Elvin-Wu/backlit-pcb-art-lamp/Images/Featured/Main-Board_Powered.jpg

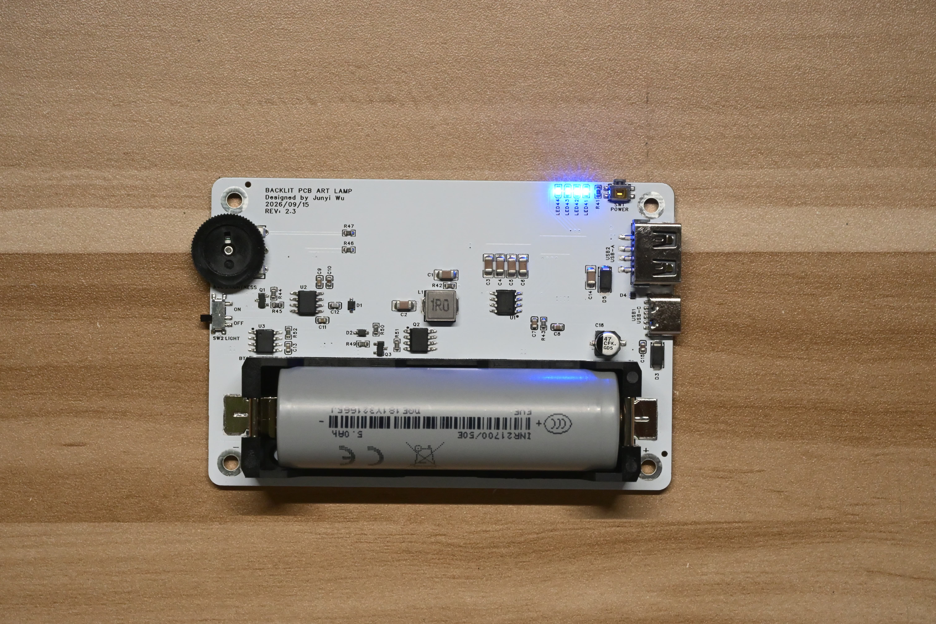
Images/Featured/Main-Board_Powered.jpg
