Elvin-Wu/backlit-pcb-art-lamp/Images/Gallery/DSC_2467.jpg

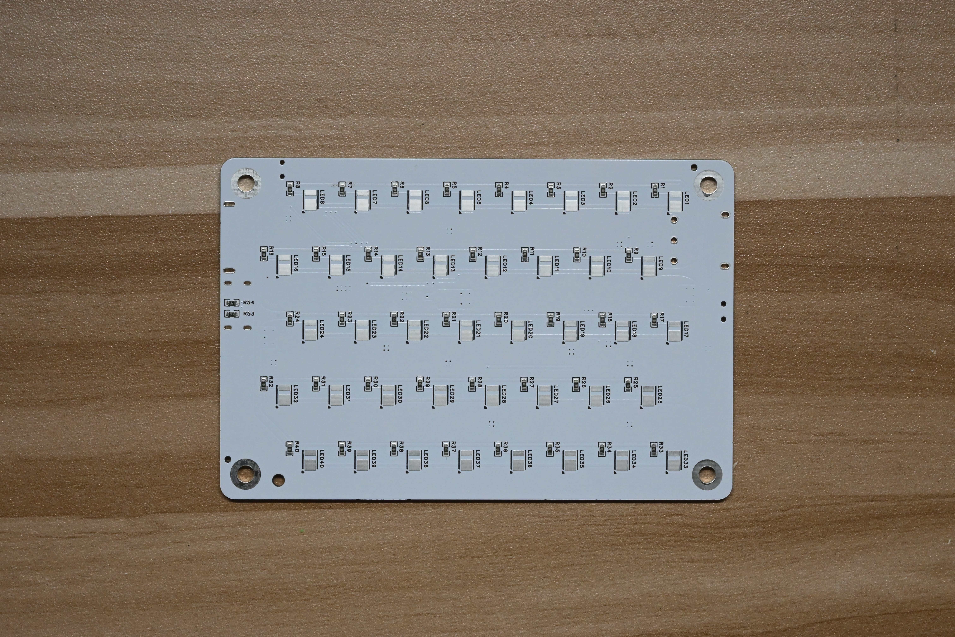
Images/Gallery/DSC_2467.jpg
