Elvin-Wu/backlit-pcb-art-lamp/Images/Gallery/DSC_2468.jpg

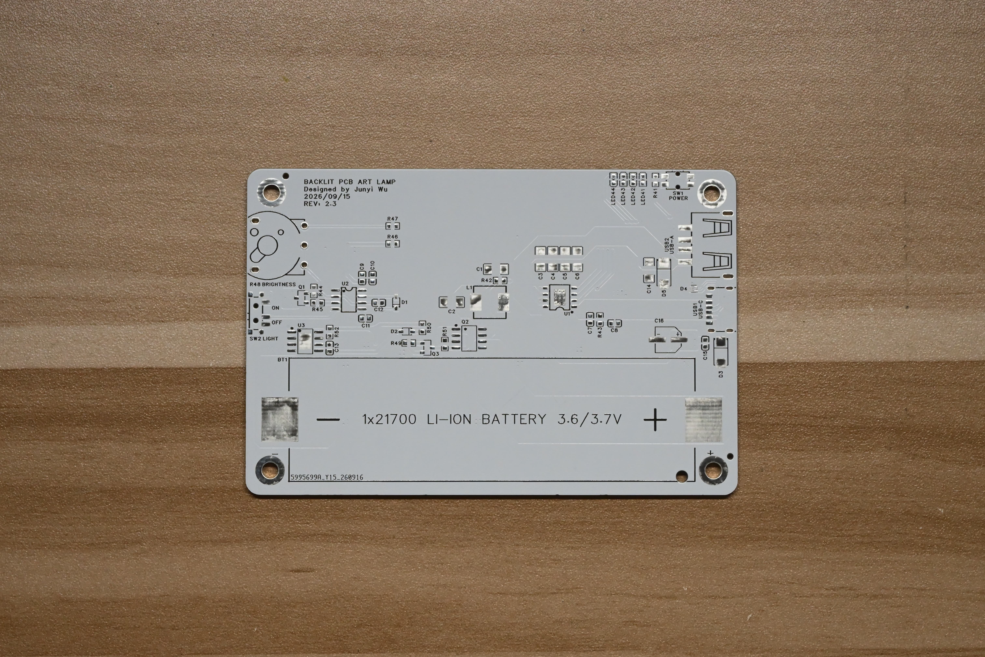
Images/Gallery/DSC_2468.jpg
