Elvin-Wu/backlit-pcb-art-lamp/Images/Gallery/DSC_2469.jpg

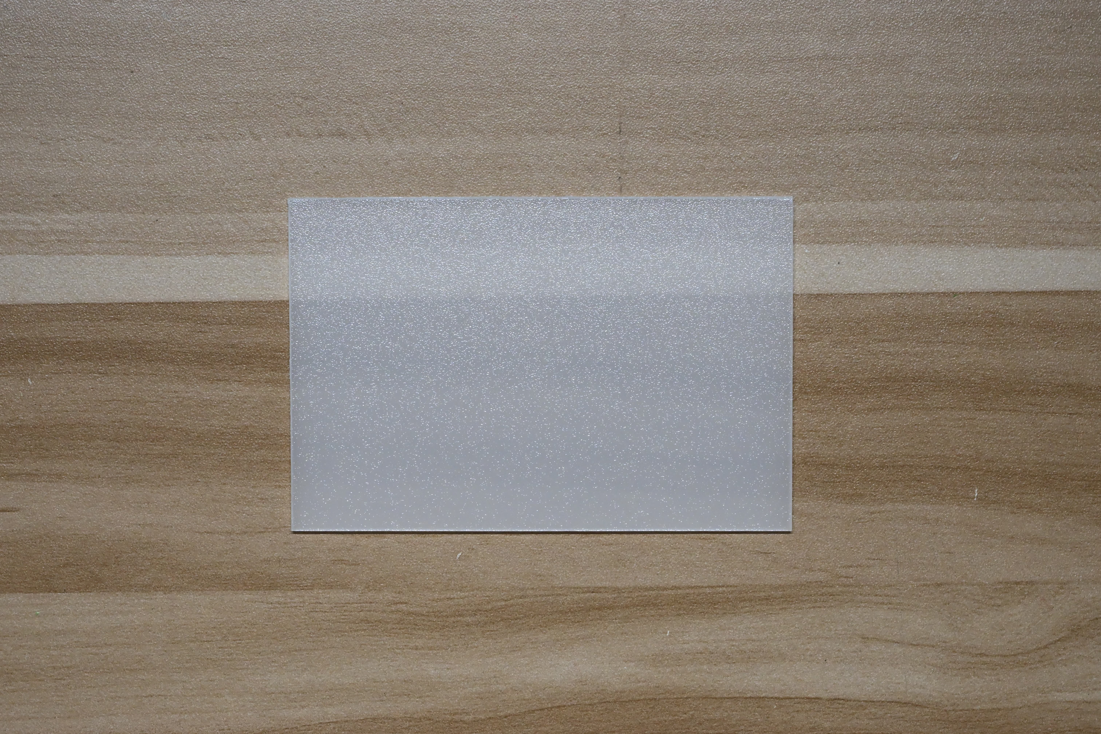
Images/Gallery/DSC_2469.jpg
