Elvin-Wu/backlit-pcb-art-lamp/Images/Gallery/DSC_2470.jpg

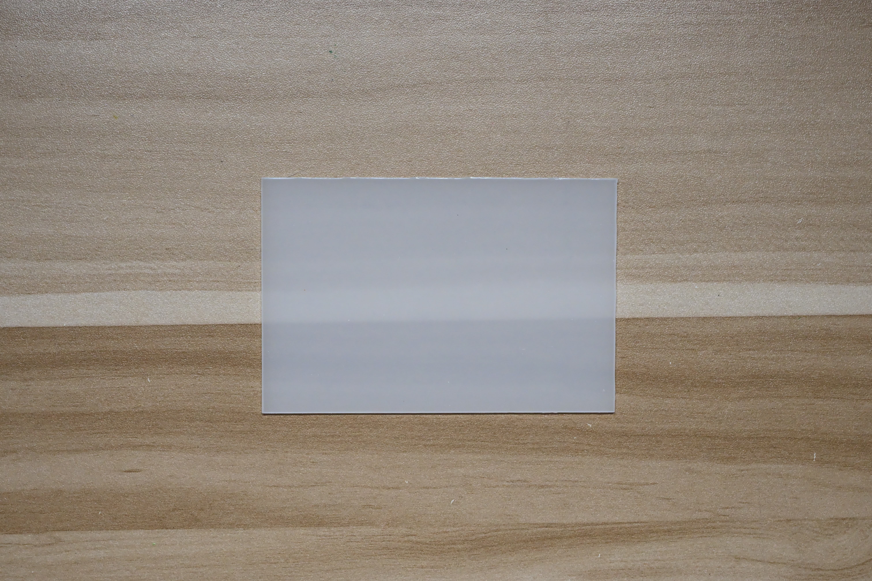
Images/Gallery/DSC_2470.jpg
