Elvin-Wu/backlit-pcb-art-lamp/Images/Gallery/DSC_2472.jpg

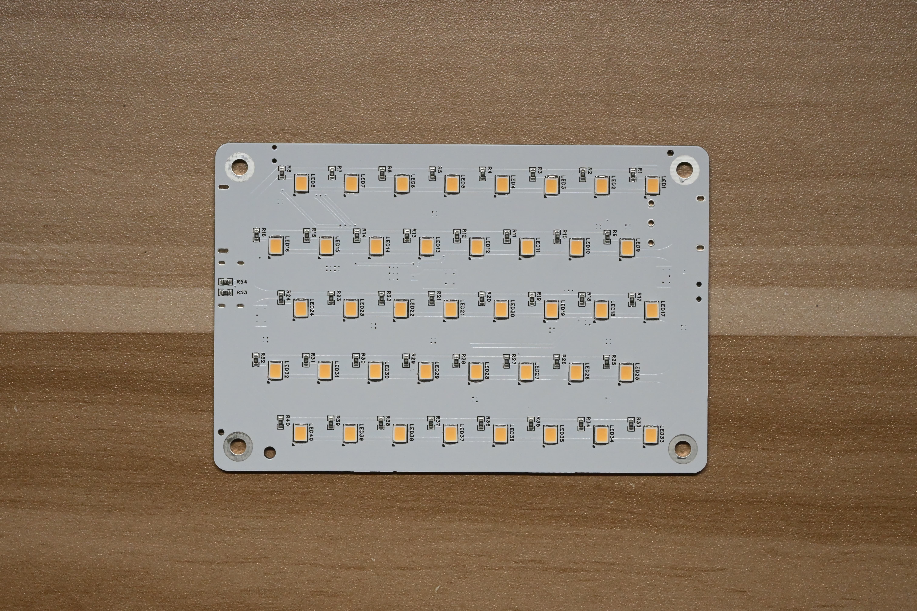
Images/Gallery/DSC_2472.jpg
