Elvin-Wu/backlit-pcb-art-lamp/Images/Gallery/DSC_2473.jpg

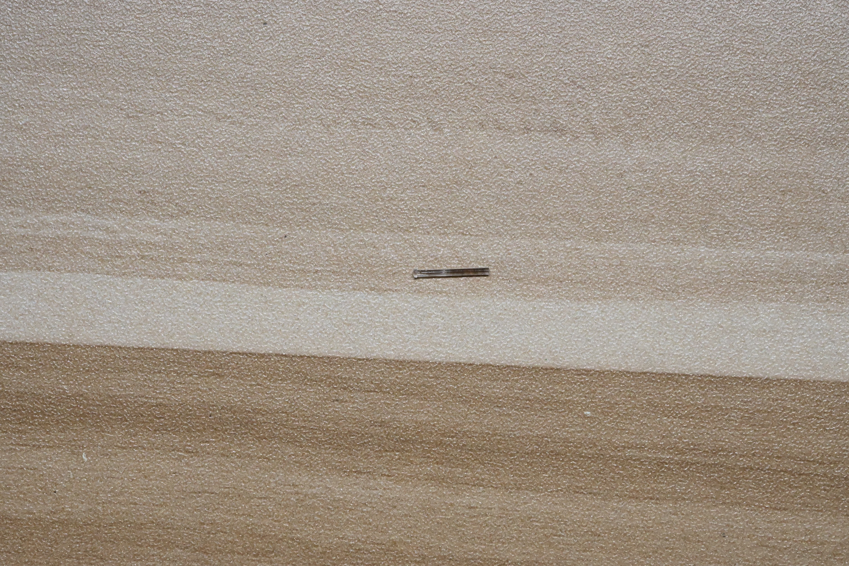
Images/Gallery/DSC_2473.jpg
