Elvin-Wu/backlit-pcb-art-lamp/Images/Gallery/DSC_2474.jpg

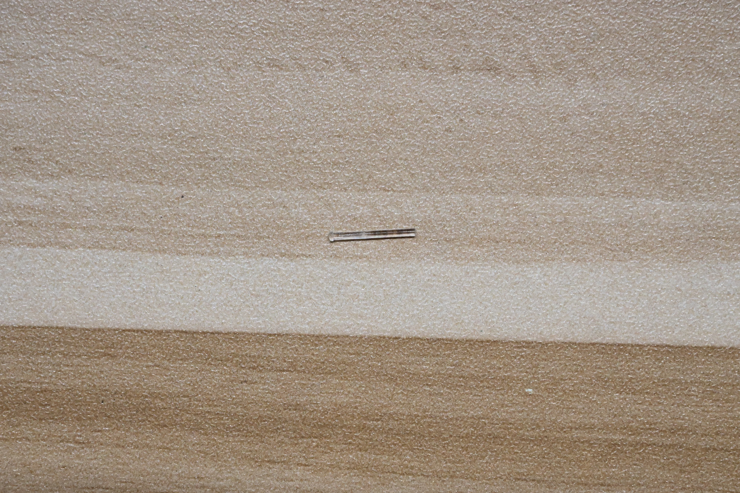
Images/Gallery/DSC_2474.jpg
