Elvin-Wu/backlit-pcb-art-lamp/Images/Gallery/DSC_2475.jpg

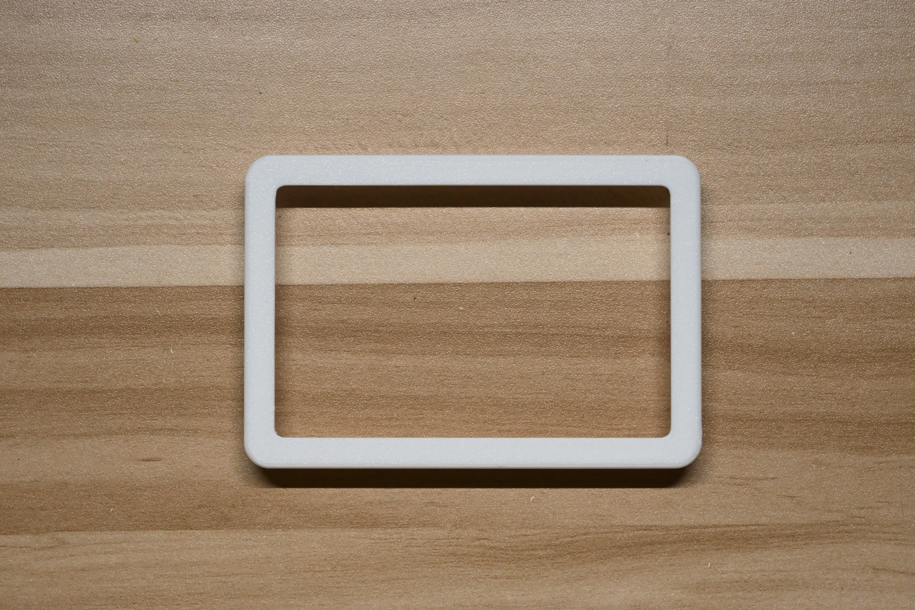
Images/Gallery/DSC_2475.jpg
