Elvin-Wu/backlit-pcb-art-lamp/Images/Gallery/DSC_2476.jpg

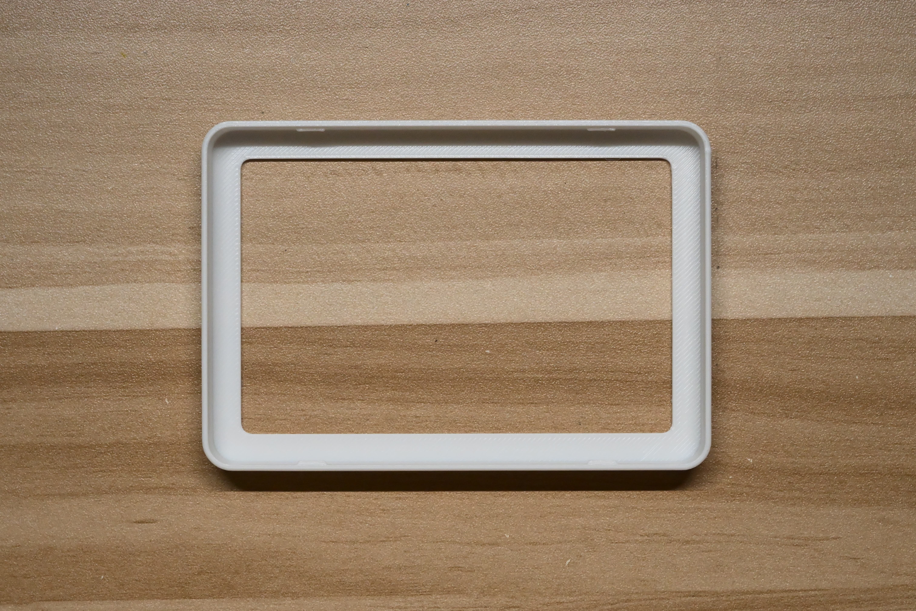
Images/Gallery/DSC_2476.jpg
