Elvin-Wu/backlit-pcb-art-lamp/Images/Gallery/DSC_2478.jpg

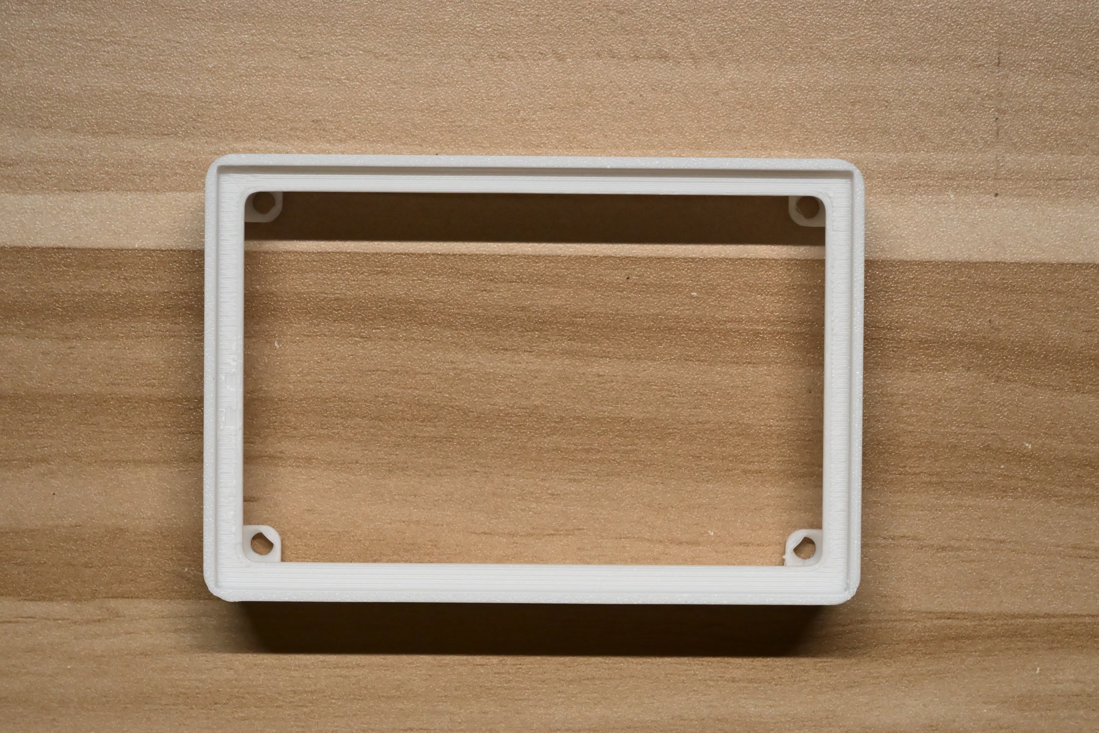
Images/Gallery/DSC_2478.jpg
