Elvin-Wu/backlit-pcb-art-lamp/Images/Gallery/DSC_2479.jpg

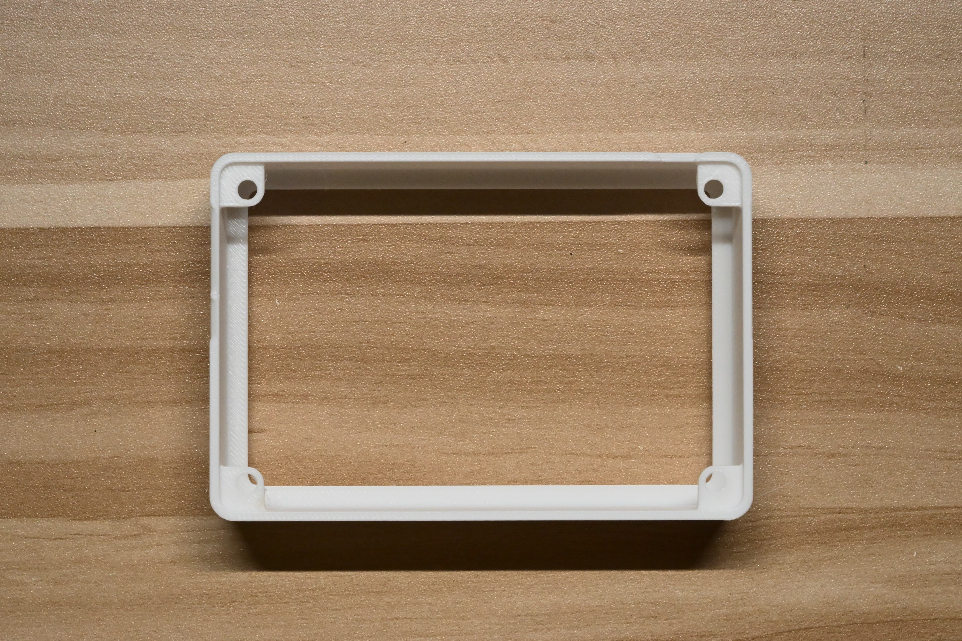
Images/Gallery/DSC_2479.jpg
