Elvin-Wu/backlit-pcb-art-lamp/Images/Gallery/DSC_2480.jpg

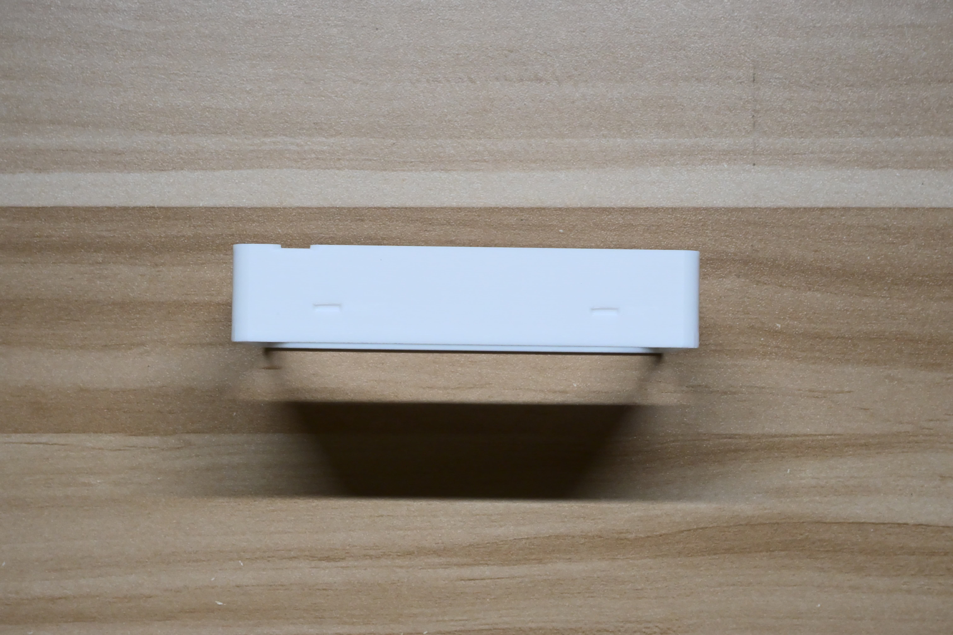
Images/Gallery/DSC_2480.jpg
