Elvin-Wu/backlit-pcb-art-lamp/Images/Gallery/DSC_2481.jpg

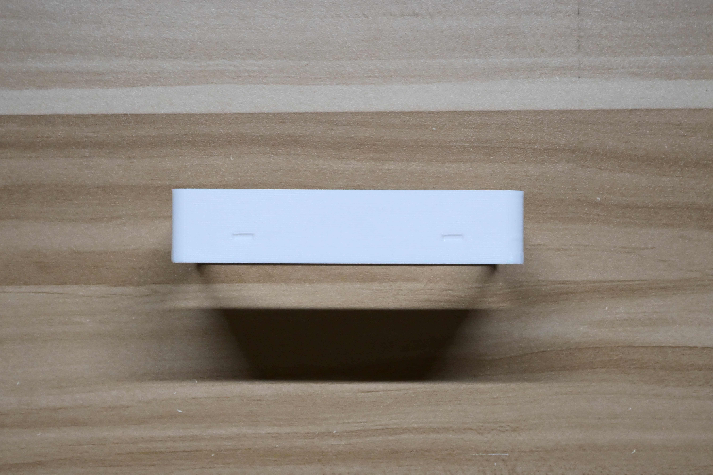
Images/Gallery/DSC_2481.jpg
