Elvin-Wu/backlit-pcb-art-lamp/Images/Gallery/DSC_2482.jpg

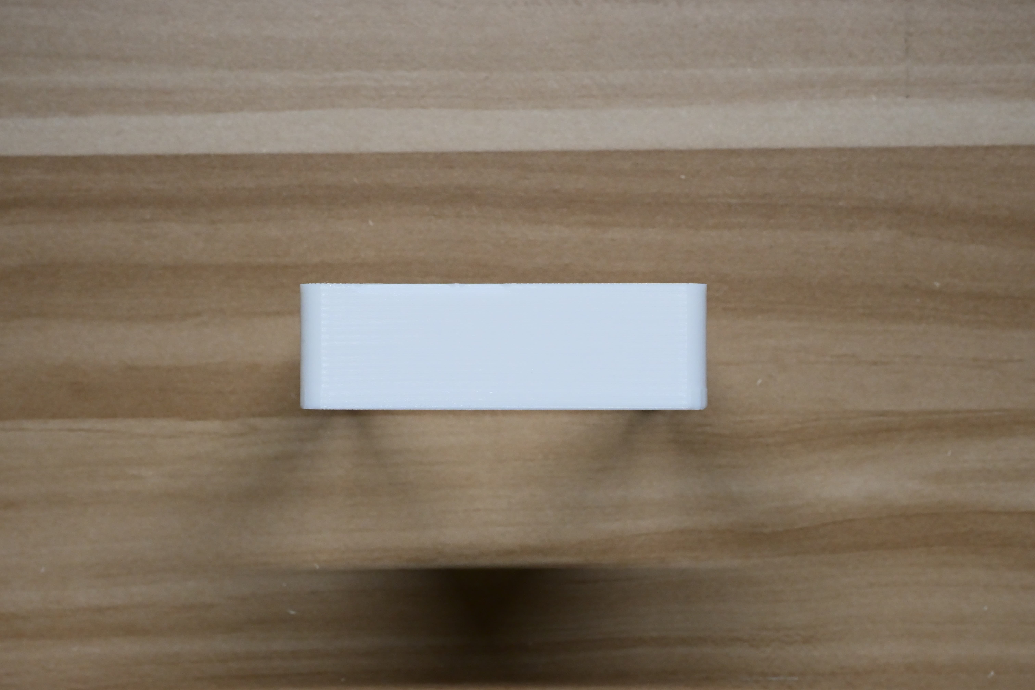
Images/Gallery/DSC_2482.jpg
