Elvin-Wu/backlit-pcb-art-lamp/Images/Gallery/DSC_2483.jpg

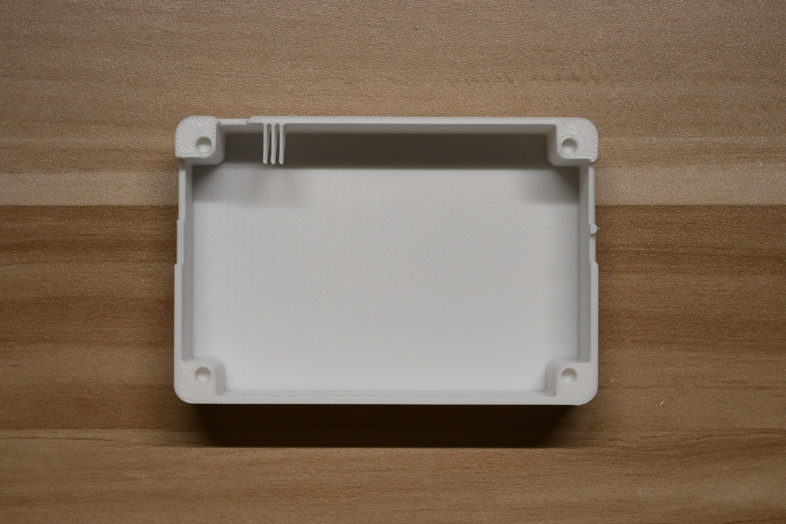
Images/Gallery/DSC_2483.jpg
