Elvin-Wu/backlit-pcb-art-lamp/Images/Gallery/DSC_2484.jpg

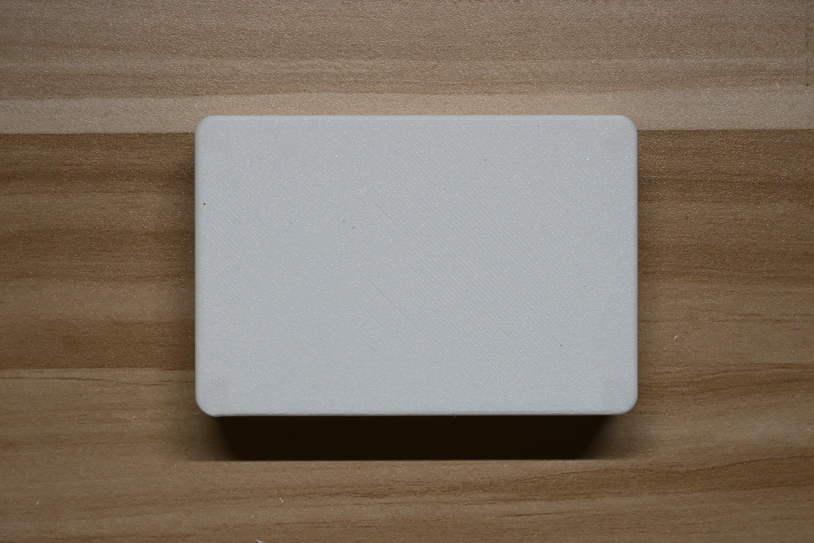
Images/Gallery/DSC_2484.jpg
