Elvin-Wu/backlit-pcb-art-lamp/Images/Gallery/DSC_2485.jpg

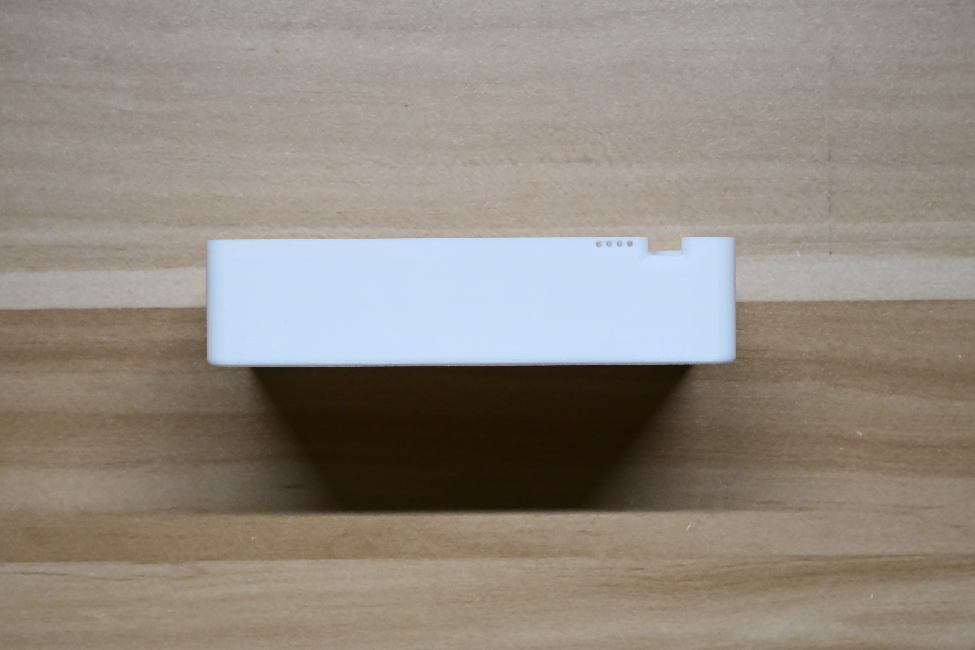
Images/Gallery/DSC_2485.jpg
