Elvin-Wu/backlit-pcb-art-lamp/Images/Gallery/DSC_2486.jpg

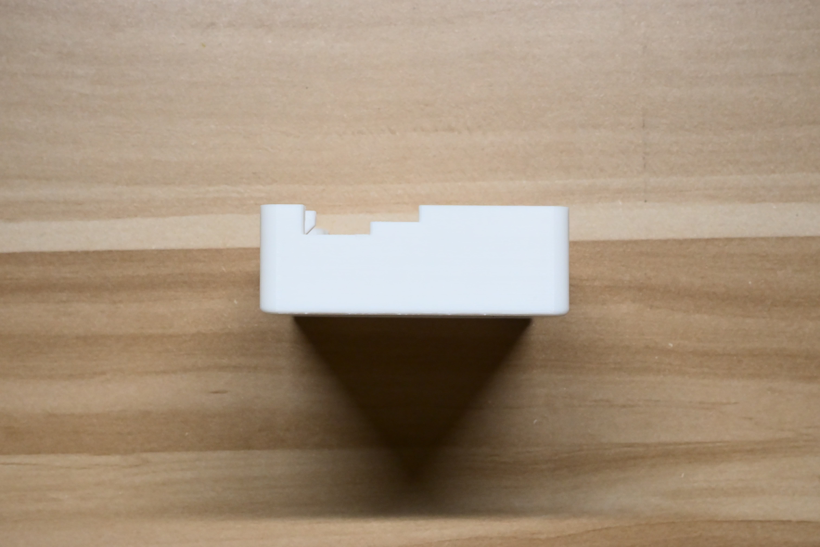
Images/Gallery/DSC_2486.jpg
