Elvin-Wu/backlit-pcb-art-lamp/Images/Gallery/DSC_2487.jpg

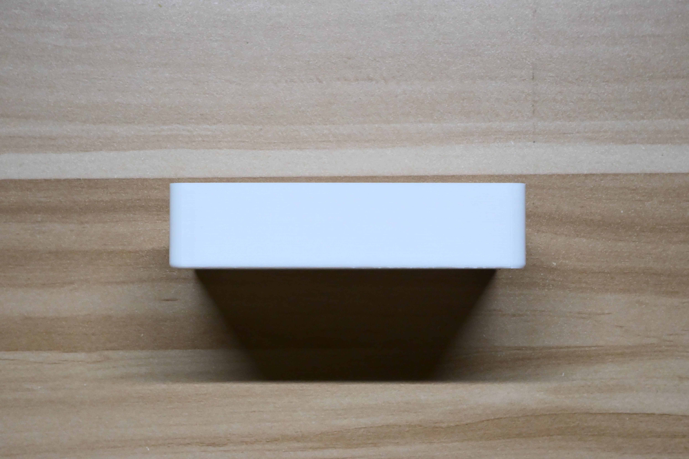
Images/Gallery/DSC_2487.jpg
