Elvin-Wu/backlit-pcb-art-lamp/Images/Gallery/DSC_2488.jpg

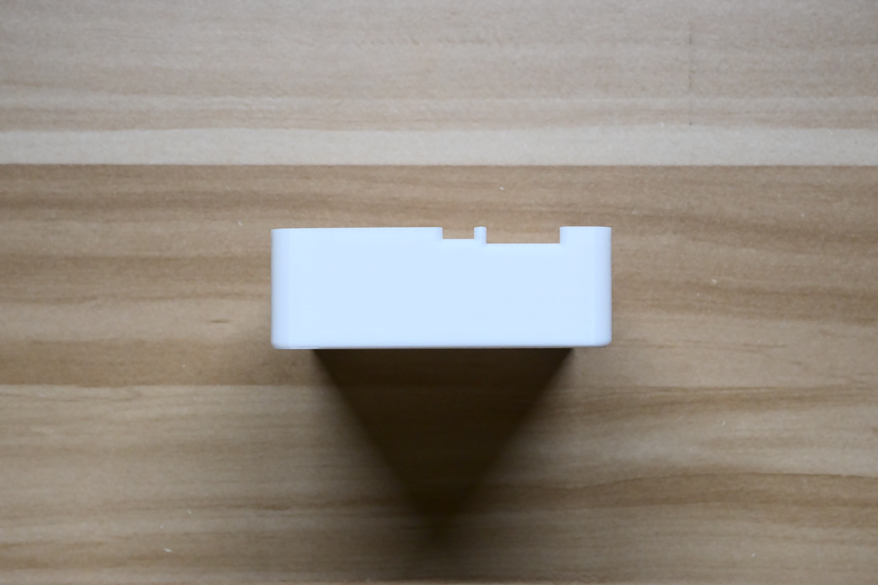
Images/Gallery/DSC_2488.jpg
