Elvin-Wu/backlit-pcb-art-lamp/Images/Gallery/DSC_2490.jpg

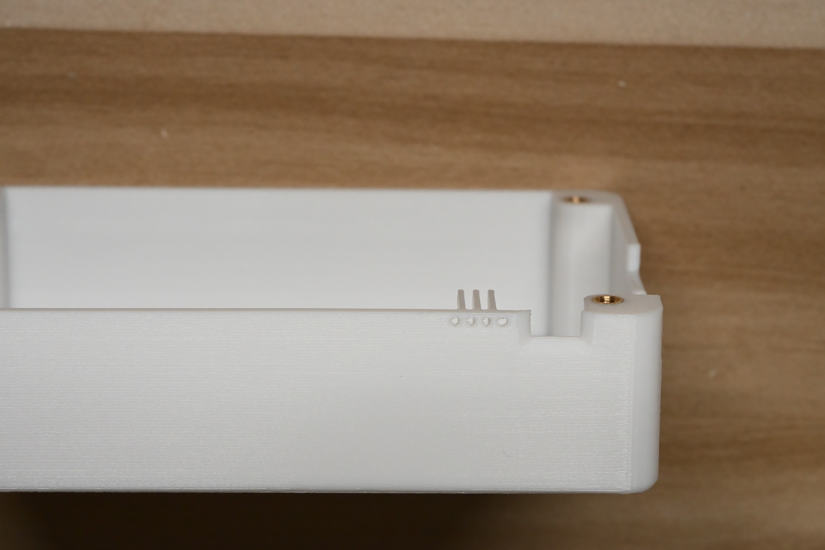
Images/Gallery/DSC_2490.jpg
