Elvin-Wu/backlit-pcb-art-lamp/Images/Gallery/DSC_2497.jpg

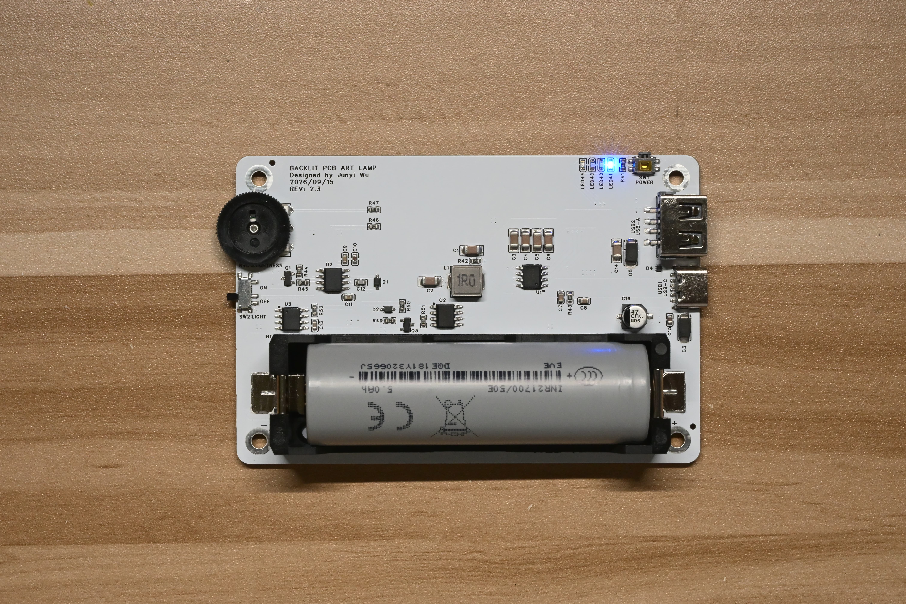
Images/Gallery/DSC_2497.jpg
