Elvin-Wu/backlit-pcb-art-lamp/Images/Gallery/DSC_2500.jpg

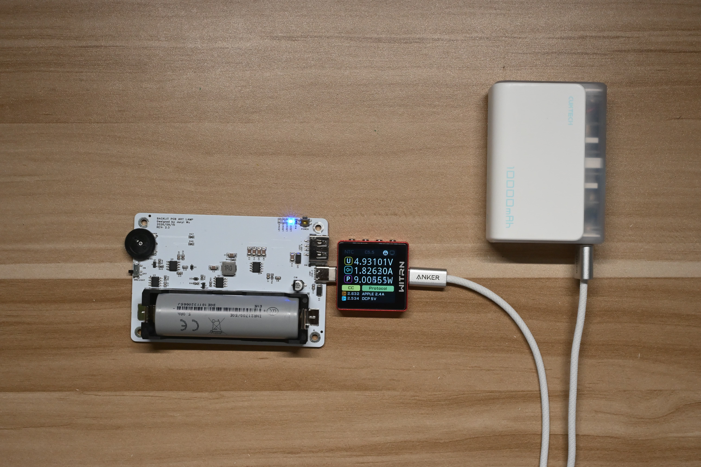
Images/Gallery/DSC_2500.jpg
