Elvin-Wu/backlit-pcb-art-lamp/Images/Gallery/DSC_2501.jpg

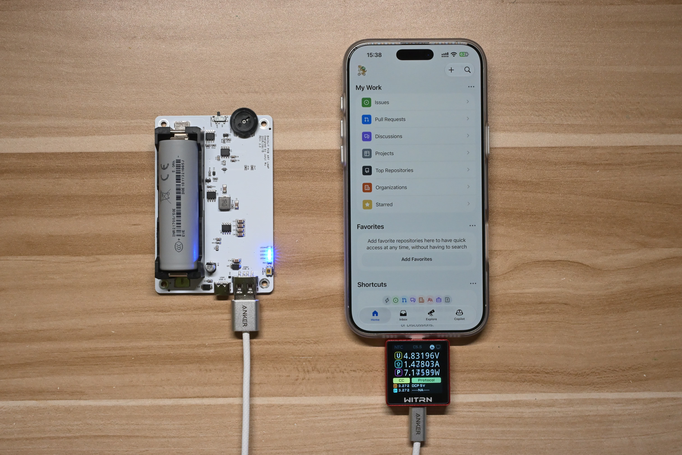
Images/Gallery/DSC_2501.jpg
