Elvin-Wu/backlit-pcb-art-lamp/Images/Gallery/DSC_2503.jpg

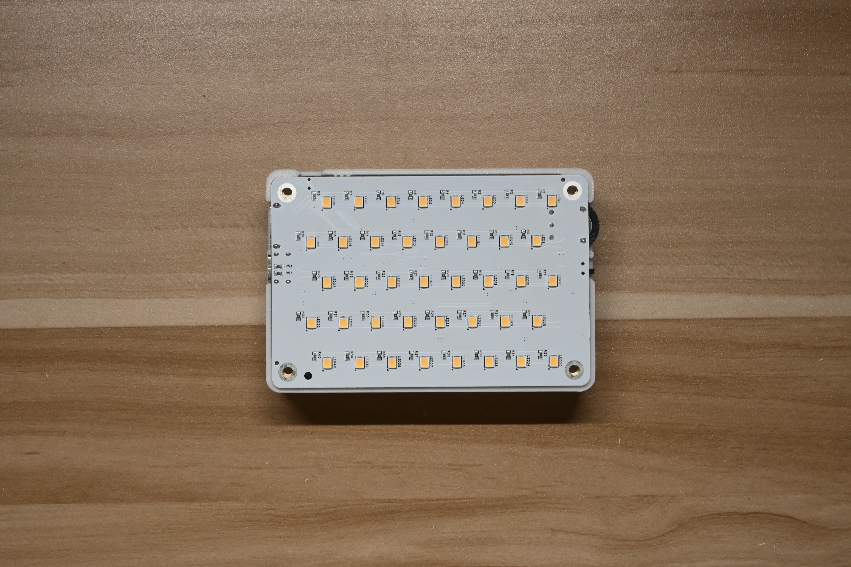
Images/Gallery/DSC_2503.jpg
