Elvin-Wu/backlit-pcb-art-lamp/Images/Gallery/DSC_2505.jpg

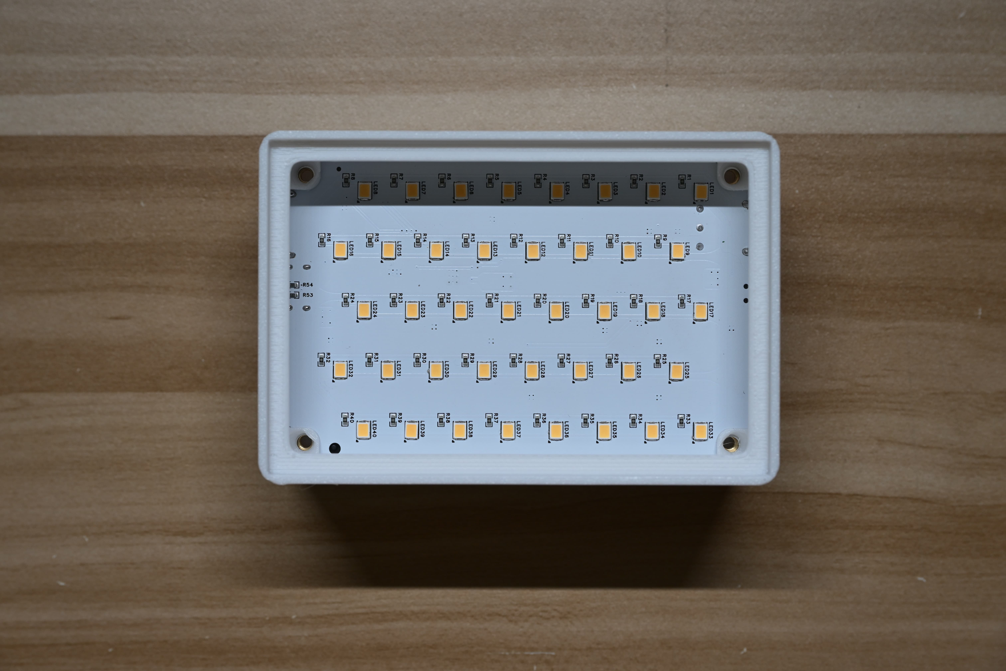
Images/Gallery/DSC_2505.jpg
