Elvin-Wu/backlit-pcb-art-lamp/Images/Gallery/DSC_2507.jpg

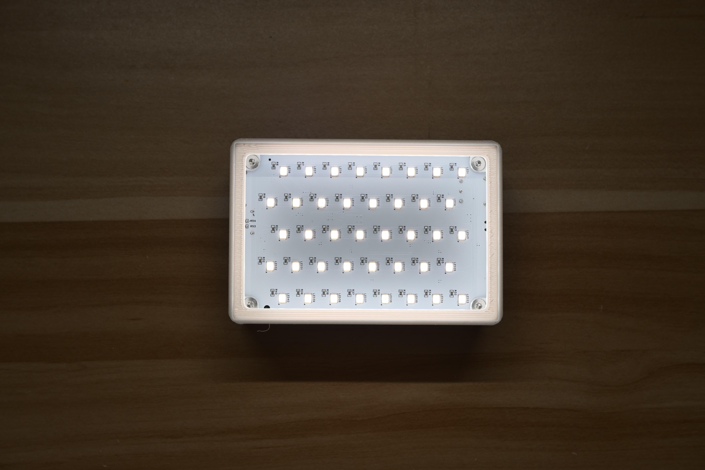
Images/Gallery/DSC_2507.jpg
