Elvin-Wu/backlit-pcb-art-lamp/Images/Gallery/DSC_2509.jpg

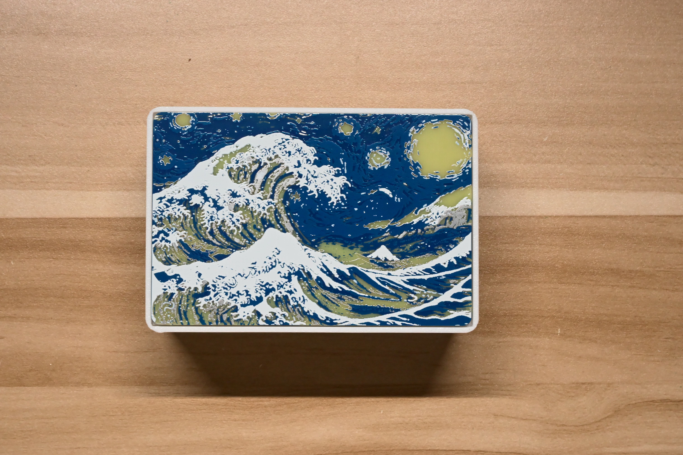
Images/Gallery/DSC_2509.jpg
