Elvin-Wu/backlit-pcb-art-lamp/Images/Gallery/DSC_2516.jpg

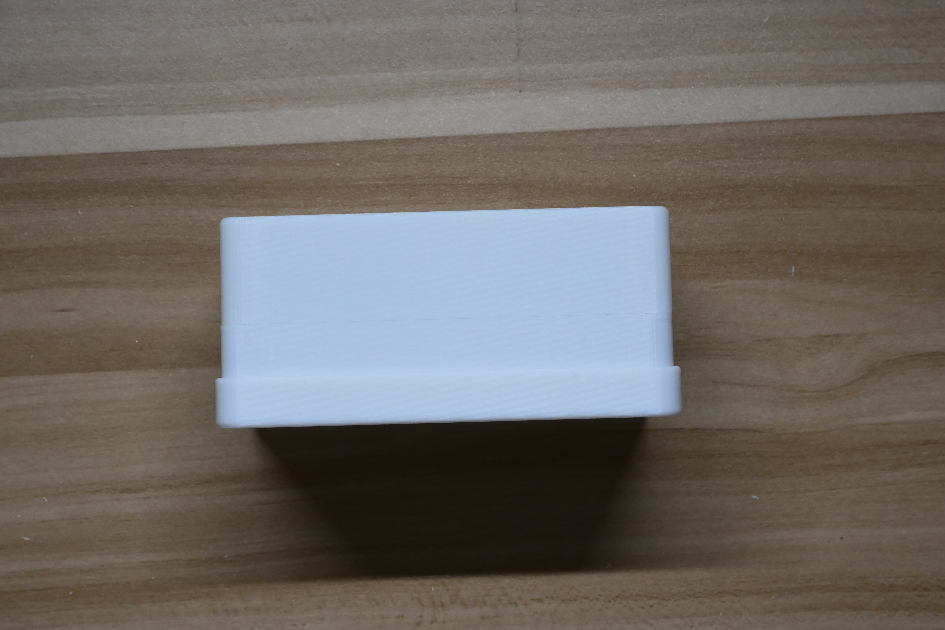
Images/Gallery/DSC_2516.jpg
