Elvin-Wu/backlit-pcb-art-lamp/Images/Gallery/DSC_2518.jpg

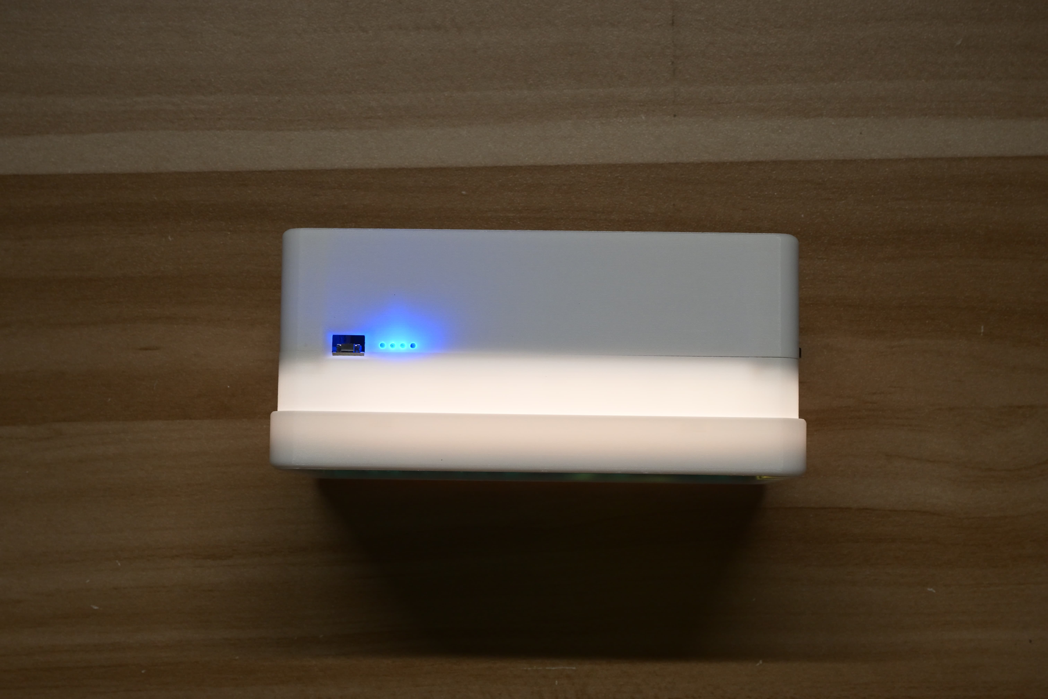
Images/Gallery/DSC_2518.jpg
