Elvin-Wu/backlit-pcb-art-lamp/Images/Gallery/DSC_2528.jpg

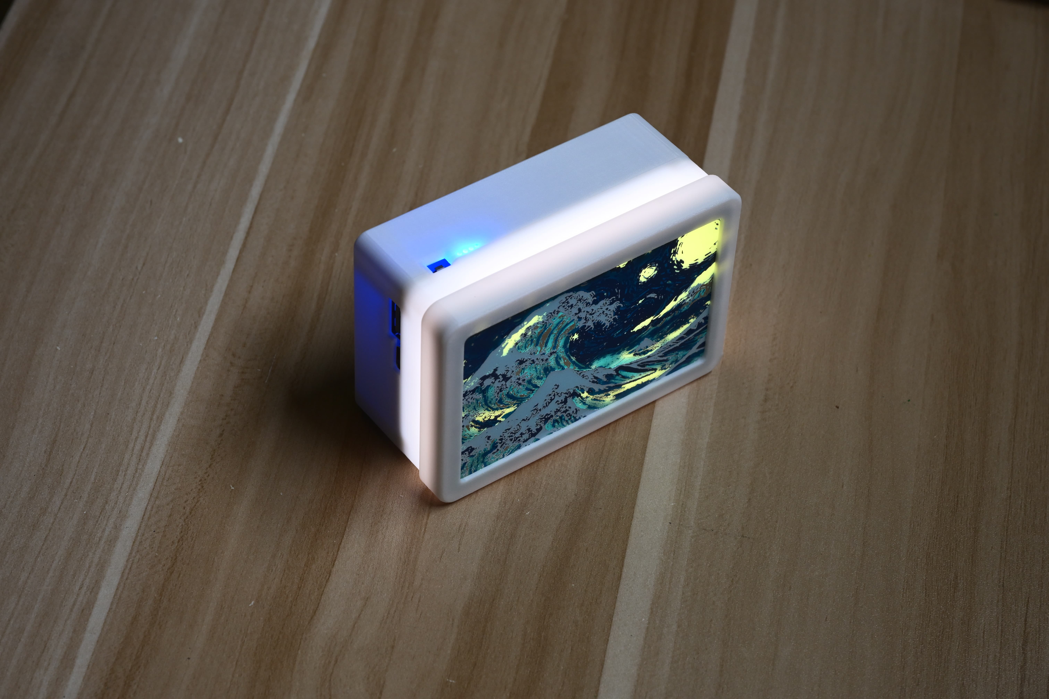
Images/Gallery/DSC_2528.jpg
